wolf-yuan-6115/kanji/firmware/include/app_config.h

#ifndef APP_CONFIG_H
#define APP_CONFIG_H

#define WIFI_SSID "YOUR_WIFI_SSID"
#define WIFI_PASSWORD "YOUR_WIFI_PASSWORD"

#define TIMEZONE_TZ "UTC0"

#define NTP_SERVER_PRIMARY "time.cloudflare.com"
#define NTP_SERVER_SECONDARY "pool.ntp.org"

#define WEATHER_URL "https://wttr.in/?format=j1"

#endif
